100prznt/MiniMacroKeyboard/src/macros.py

# --- Makrotexte fuer das Makro-Keyboard ---
# Ausgelagert aus code.py, damit die Texte separat gepflegt werden koennen,
# ohne die eigentliche Ablauflogik anzufassen.

TEXT_M2 = "M2"

# Wird bei der Tastenkombo M1+M3 ausgegeben (nur bei passender Anwendung
# oder gesperrtem PC) - siehe Combo-Logik in code.py.
TEXT_M4 = "M4"

# --- TODO-Kommentar (M1): Name fuer die erste Zeile ---
TODO_SIGNATURE = "Max Mustermann"
